TemuWolverine/SparkleBoard/plots/pcb_back.png

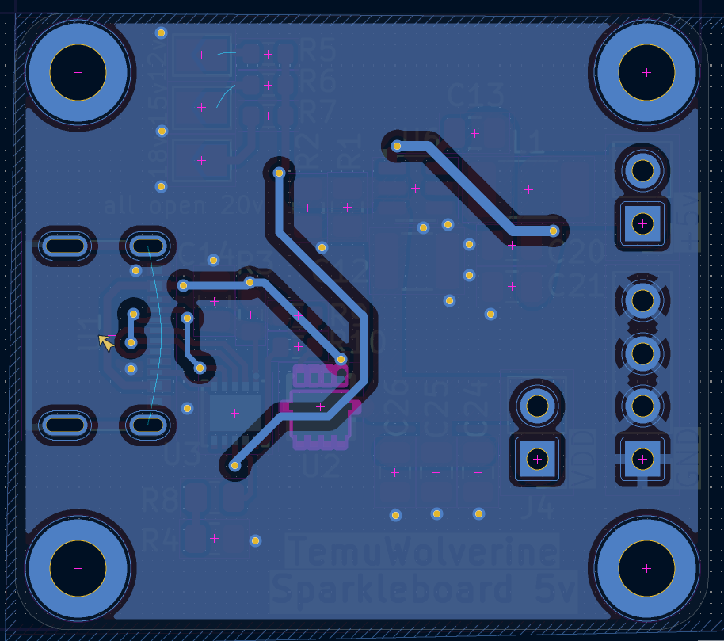
plots/pcb_back.png
