TemuWolverine/SparkleBoard/plots/USB-PD.png

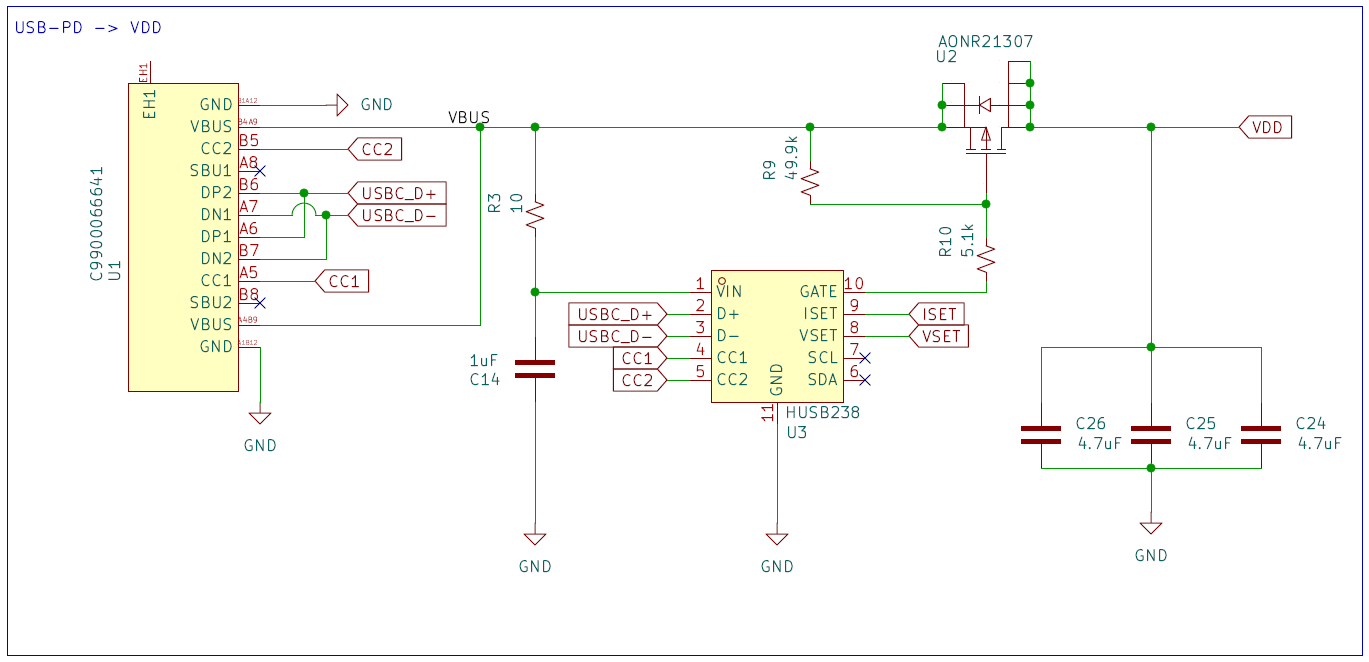
plots/USB-PD.png
